xpix/XStepper/eagle3d/XStepper_mini.jpg

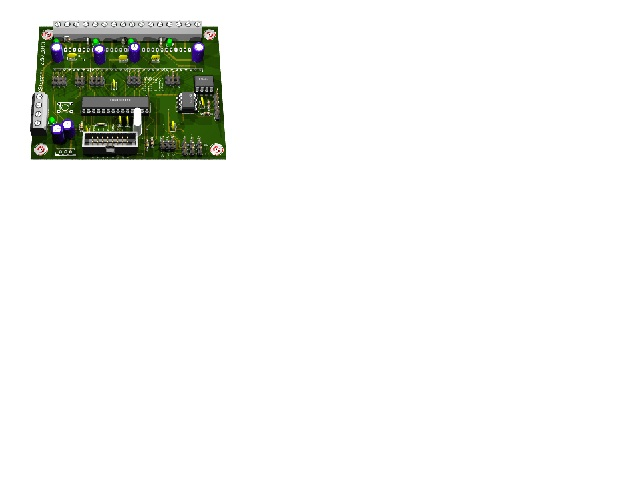
eagle3d/XStepper_mini.jpg
