xpix/XStepper/eagleUp/eagleUp_XStepper_board_bottom.png

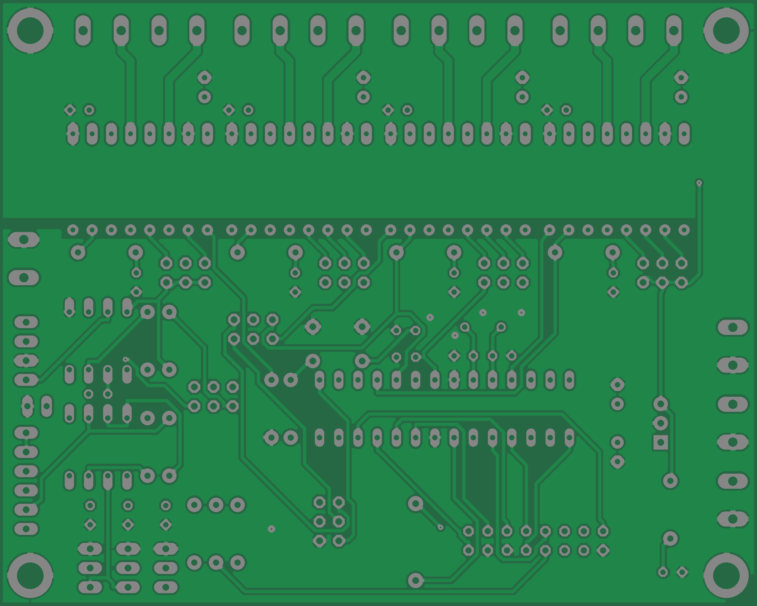
eagleUp/eagleUp_XStepper_board_bottom.png
