xpix/XStepper/eagleUp/eagleUp_XStepper_board_top.png

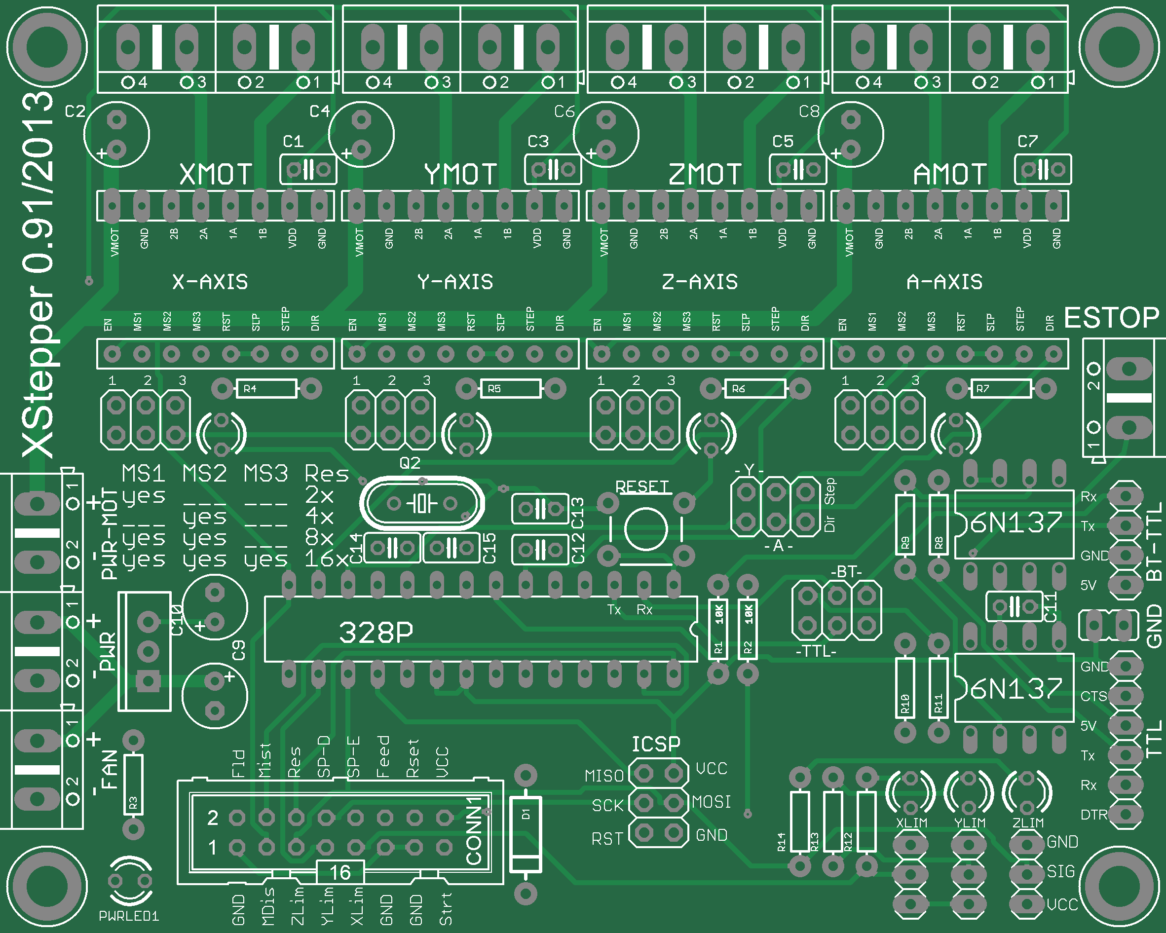
eagleUp/eagleUp_XStepper_board_top.png
