xpix/XStepper/eagleUp/eagleUp_XStepper_bottom.png

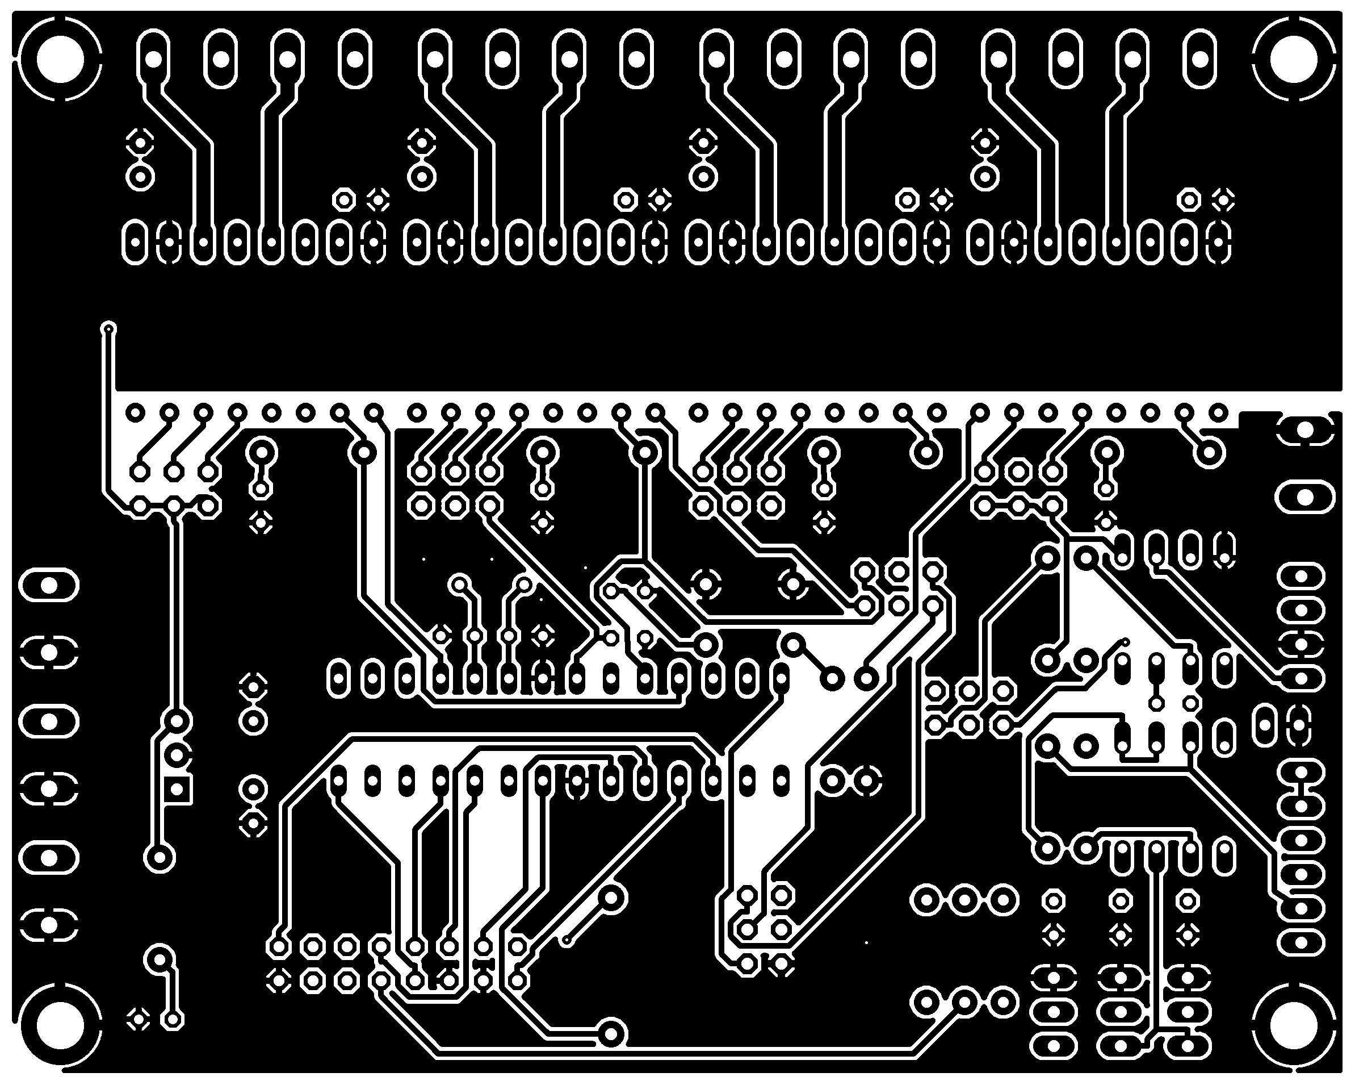
eagleUp/eagleUp_XStepper_bottom.png
