xpix/XStepper/eagleUp/eagleUp_XStepper_imagesize.png

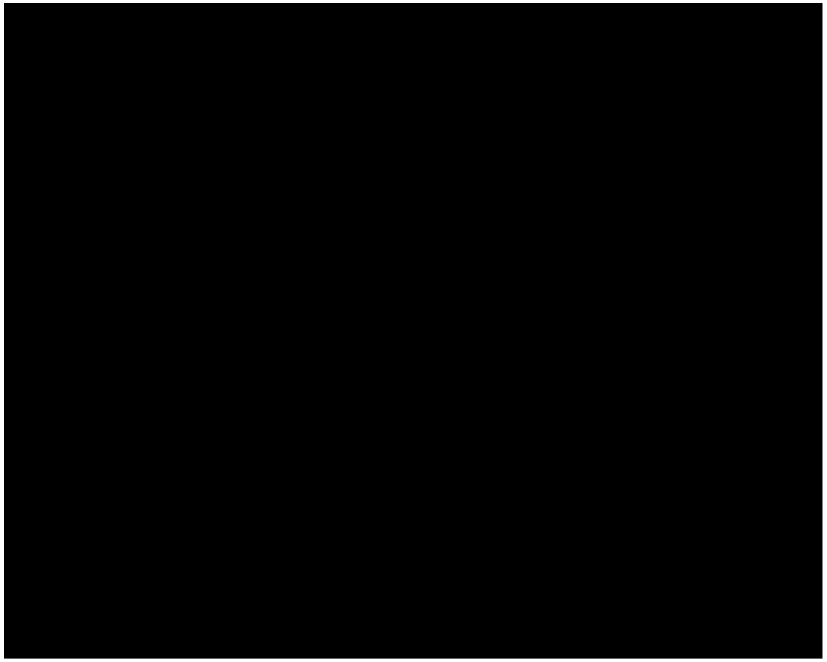
eagleUp/eagleUp_XStepper_imagesize.png
