xpix/XStepper/eagleUp/eagleUp_XStepper_outline.png

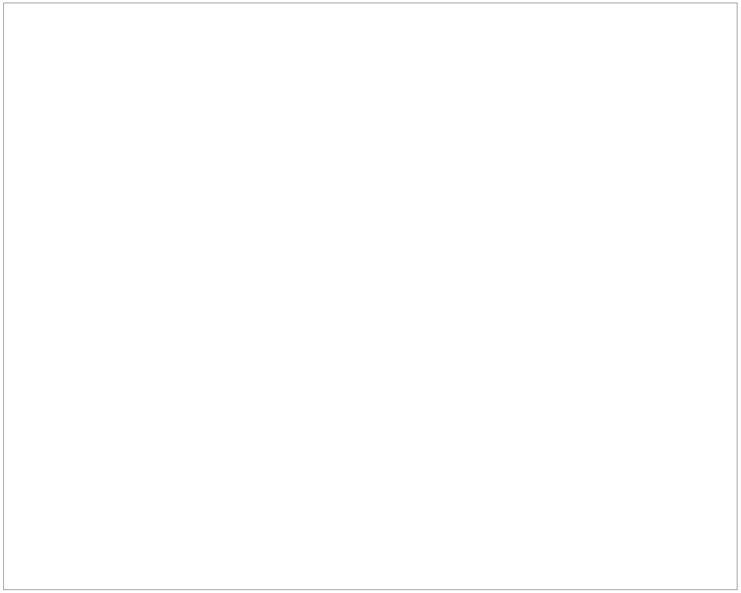
eagleUp/eagleUp_XStepper_outline.png
