xpix/XStepper/eagleUp/XStepper.png

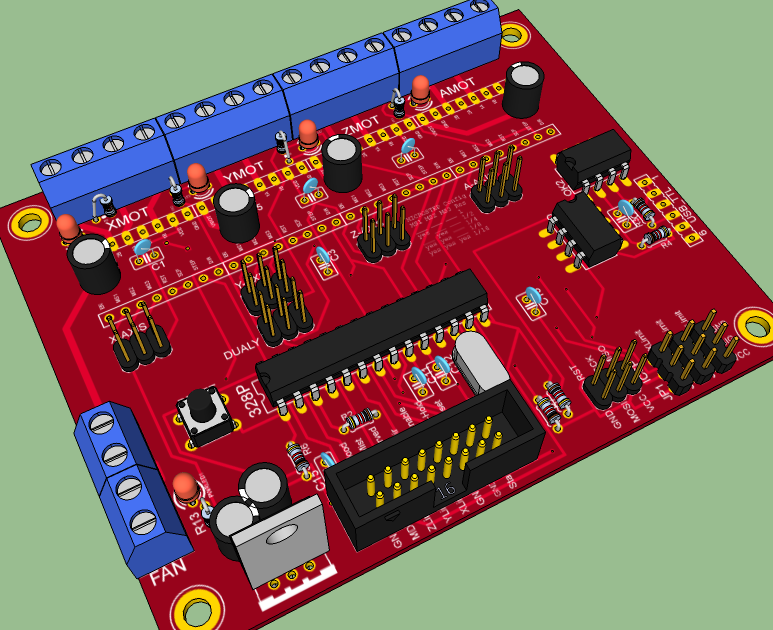
eagleUp/XStepper.png
